DriftSolutions/AlarmClock/Output/resources/images/back.png

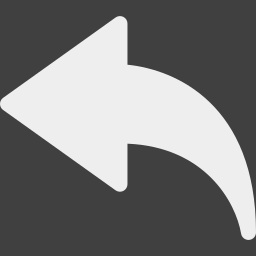
Output/resources/images/back.png
