DriftSolutions/AlarmClock/Output/resources/images/clock.png

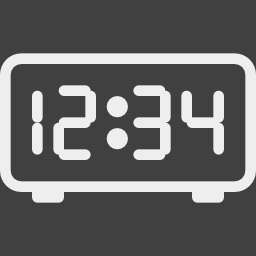
Output/resources/images/clock.png
