DriftSolutions/AlarmClock/Output/resources/images/down.png

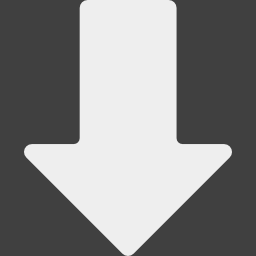
Output/resources/images/down.png
