DriftSolutions/AlarmClock/Output/resources/images/settings.png

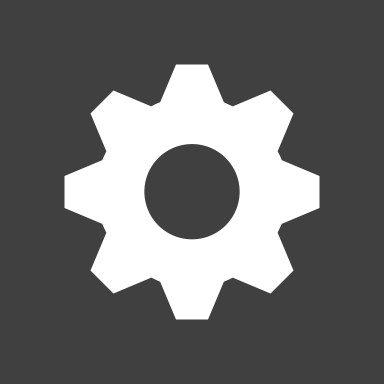
Output/resources/images/settings.png
