DriftSolutions/AlarmClock/Output/resources/images/up.png

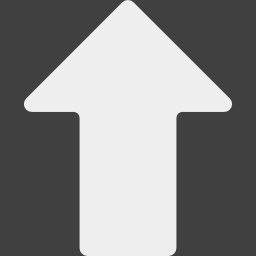
Output/resources/images/up.png
